Longan-Labs/Longan_Core_01_Resources/images/1040008-4.jpg

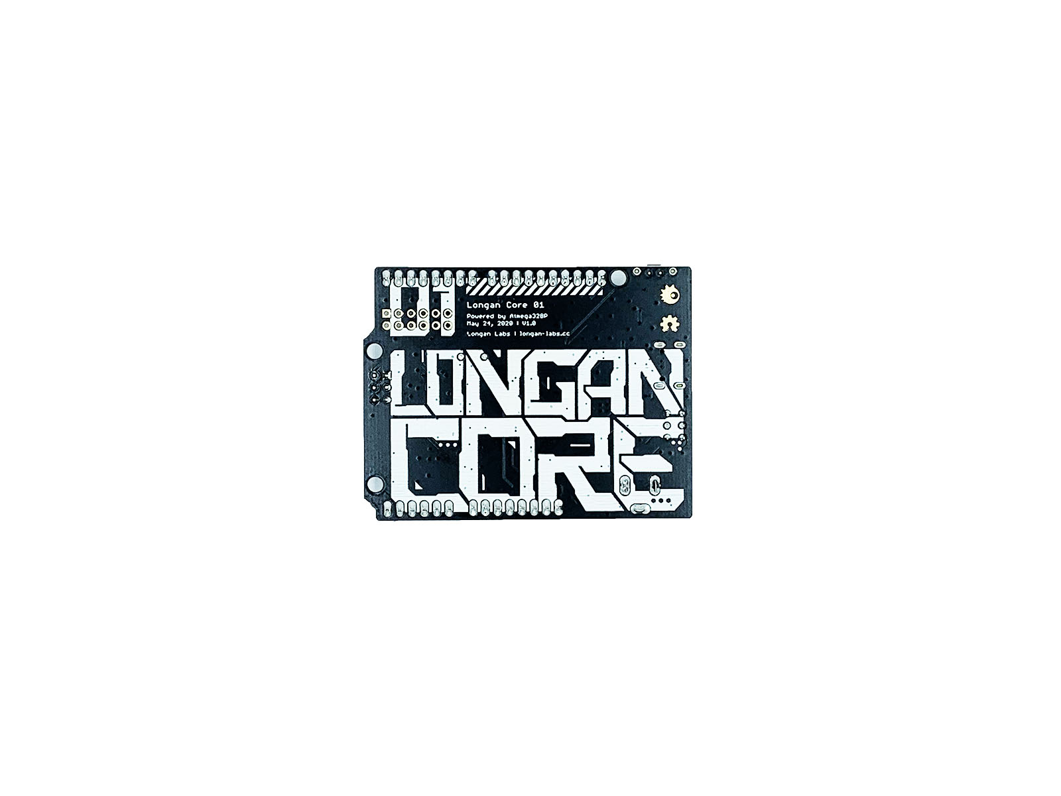
images/1040008-4.jpg
